mocona05/Lattepanda-Measurement-Shield/STM32/User/cli.h

#pragma once
#include <stdbool.h>
//extern bool cliMode;






//void cliProcess(void);
//void Mavlink(void);
void serial_direct_can_bus(void);
void mavlink_interval_send_test(void);
void Mavlink_handller(void);
